TheBlueManCoding/ModularControlPanel/src/src/SecretSettings.example.h

#ifndef SecretSettingsH
#define SecretSettingsH

#define WIFI_SSID     "yourssid"
#define WIFI_PASSWORD "yourpassword"
#define MQTT_IP       "192.168.0.45"
#define MQTT_PORT     1883
#define OWN_IP        "" // use dhcp

#endif // SecretSettingsH
